RidDleZ33/Ratrig-VC3.1-EazyIDEX/Crossbow_Cutter_Mods/VC4_Depressor/vc4_y_bumper_depressor_v2_2.png

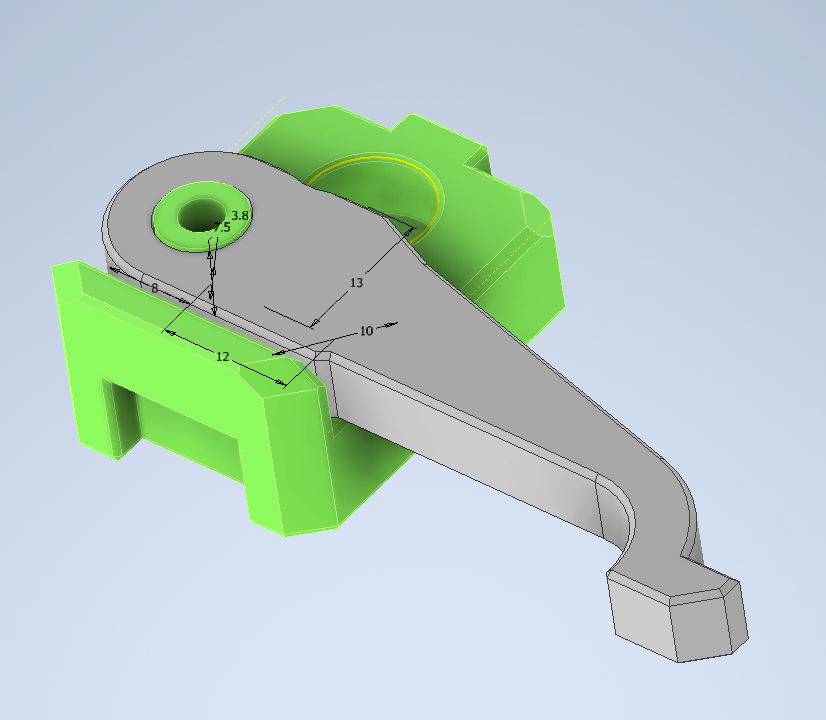
Crossbow_Cutter_Mods/VC4_Depressor/vc4_y_bumper_depressor_v2_2.png
