RidDleZ33/Ratrig-VC3.1-EazyIDEX/Crossbow_Cutter_Mods/VC4_LGX_LITE/20260310_191639.jpg

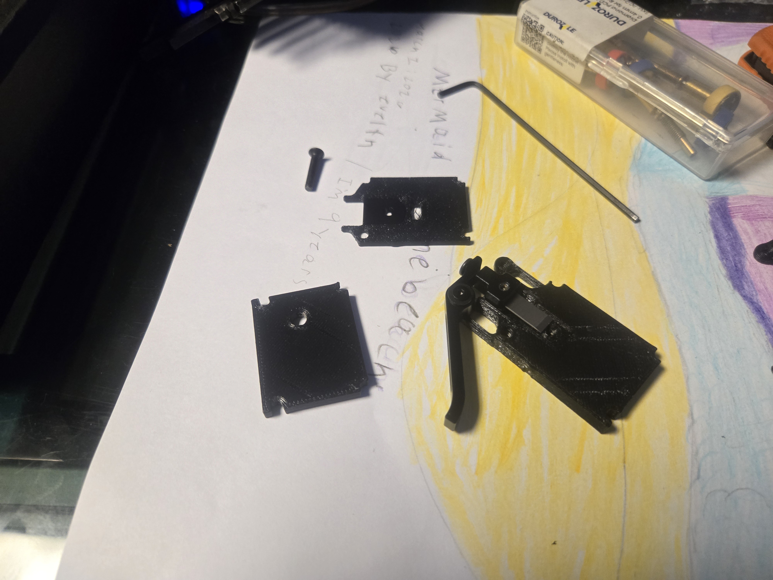
Crossbow_Cutter_Mods/VC4_LGX_LITE/20260310_191639.jpg
