RidDleZ33/Ratrig-VC3.1-EazyIDEX/Crossbow_Cutter_Mods/VC4_LGX_LITE/Cutter_VC4_LGX_LITE_ASSY2.png

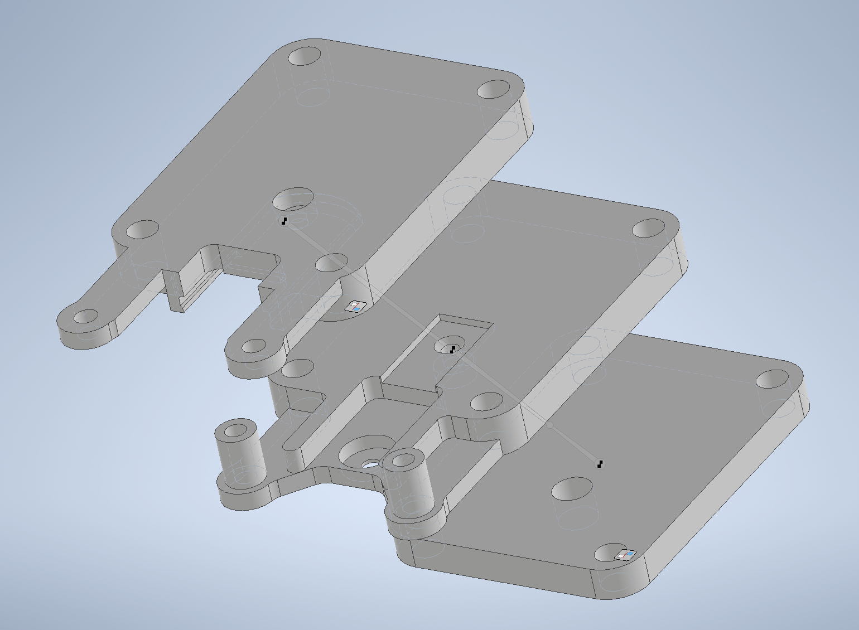
Crossbow_Cutter_Mods/VC4_LGX_LITE/Cutter_VC4_LGX_LITE_ASSY2.png
