RidDleZ33/Ratrig-VC3.1-EazyIDEX/RR_Toolhead_Mods/LGx_Lite_Adapter_MOD/LGx_Lite_REVO1.png

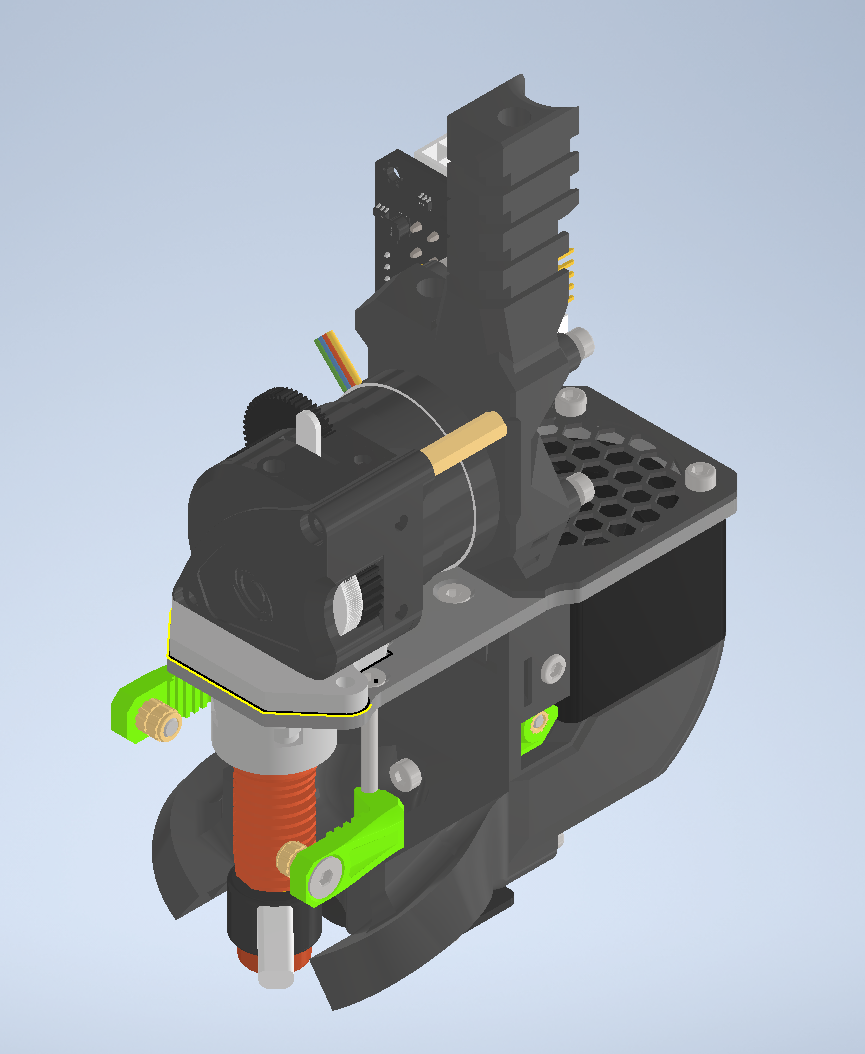
RR_Toolhead_Mods/LGx_Lite_Adapter_MOD/LGx_Lite_REVO1.png
