RidDleZ33/Ratrig-VC3.1-EazyIDEX/3_4_Hybrid/Alum/vc4_xy_joiner_upper_v1.1 v1.stl

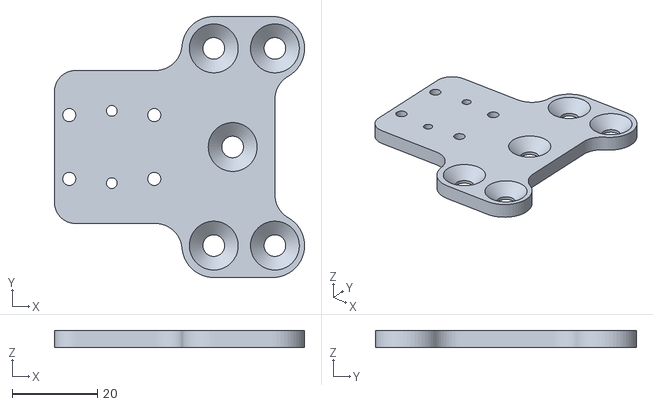
[picture p33: CAD file, 2024-08-03]
3_4_Hybrid/Alum/vc4_xy_joiner_upper_v1.1 v1.stl
58.9 x 61.4 x 4.00
