RidDleZ33/Ratrig-VC3.1-EazyIDEX/Crossbow_Cutter_Mods/VC4_LGX_LITE/Crossbow CNC VC4_LGX_LITE_UNI_V2_Body.stl

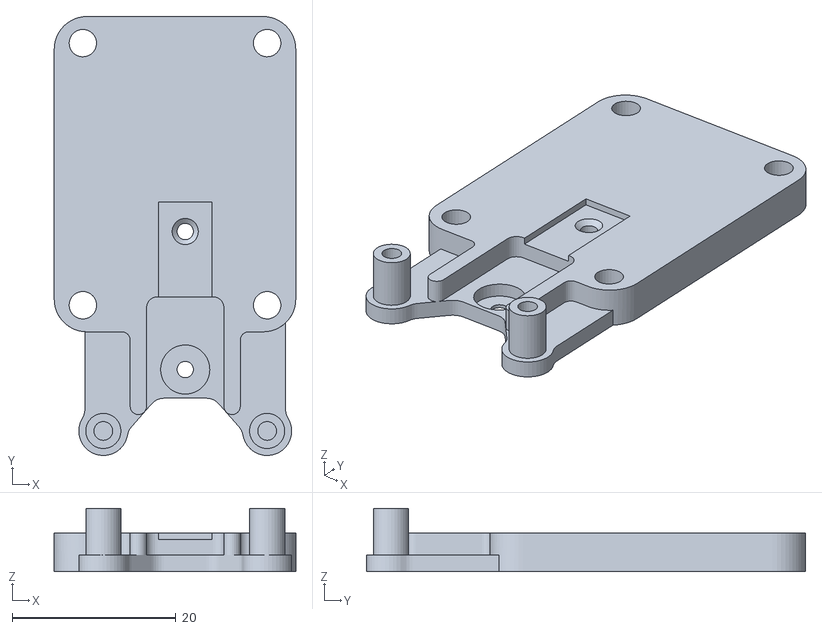
[picture p34: CAD file, 2026-04-05]
Crossbow_Cutter_Mods/VC4_LGX_LITE/Crossbow CNC VC4_LGX_LITE_UNI_V2_Body.stl
29.5 x 53.6 x 7.70
