RidDleZ33/Ratrig-VC3.1-EazyIDEX/VC3.1_Stock/EazyIDEX_enclosure2_xy_idlers_right_idex_3.1.stl

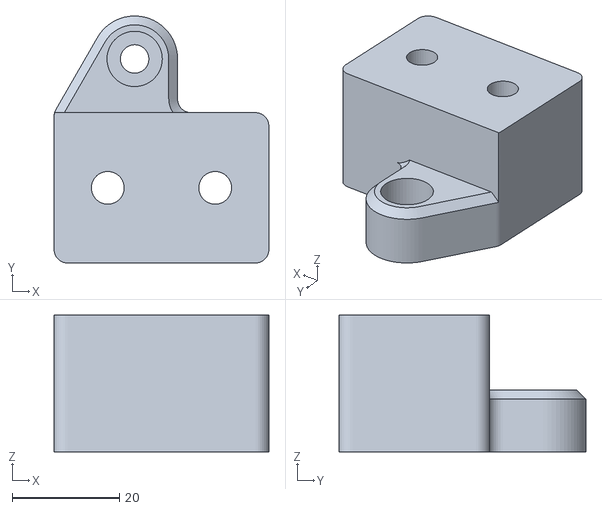
[picture p35: CAD file, 2024-07-27]
VC3.1_Stock/EazyIDEX_enclosure2_xy_idlers_right_idex_3.1.stl
40.0 x 46.0 x 25.5
