RidDleZ33/Ratrig-VC3.1-EazyIDEX/3_4_Hybrid/Alum/EazyIDEX34_vc4_tensioner_body_left_v1.0 v1.stl

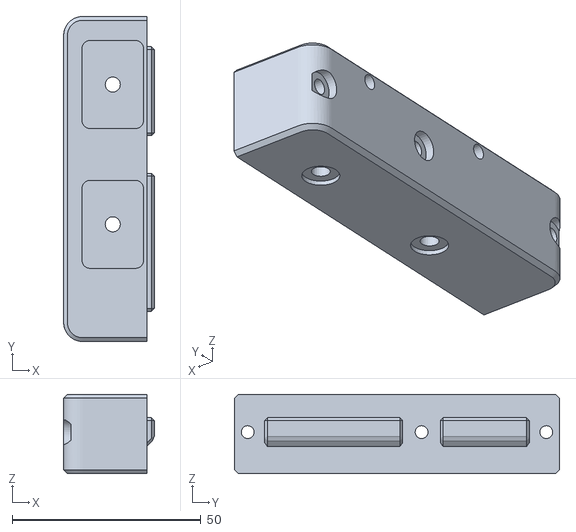
[picture p36: CAD file, 2024-08-03]
3_4_Hybrid/Alum/EazyIDEX34_vc4_tensioner_body_left_v1.0 v1.stl
24.0 x 86.0 x 21.0
