RidDleZ33/Ratrig-VC3.1-EazyIDEX/3_4_Hybrid/vc4_x_endstop v1.stl

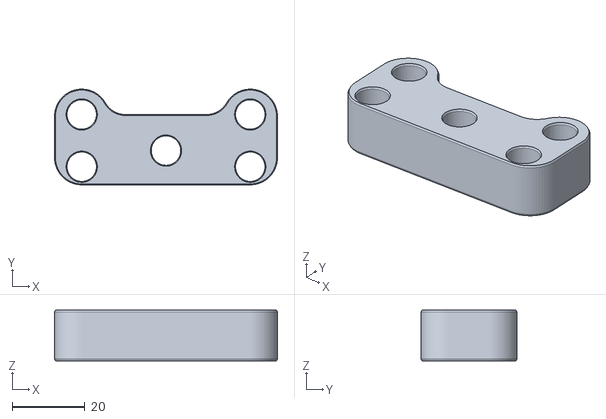
[picture p37: CAD file, 2024-08-03]
3_4_Hybrid/vc4_x_endstop v1.stl
61.4 x 26.4 x 14.0
