RidDleZ33/Ratrig-VC3.1-EazyIDEX/3_4_Hybrid/vc4_y_bumper v1.stl

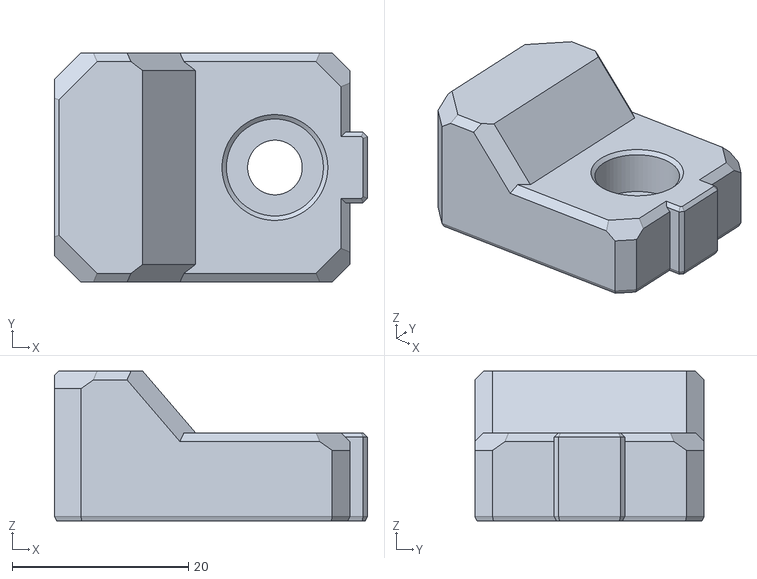
[picture p38: CAD file, 2024-08-03]
3_4_Hybrid/vc4_y_bumper v1.stl
35.5 x 26.0 x 17.0
