RidDleZ33/Ratrig-VC3.1-EazyIDEX/VC3.1_Stock/EazyIDEX_joiner_left.stl

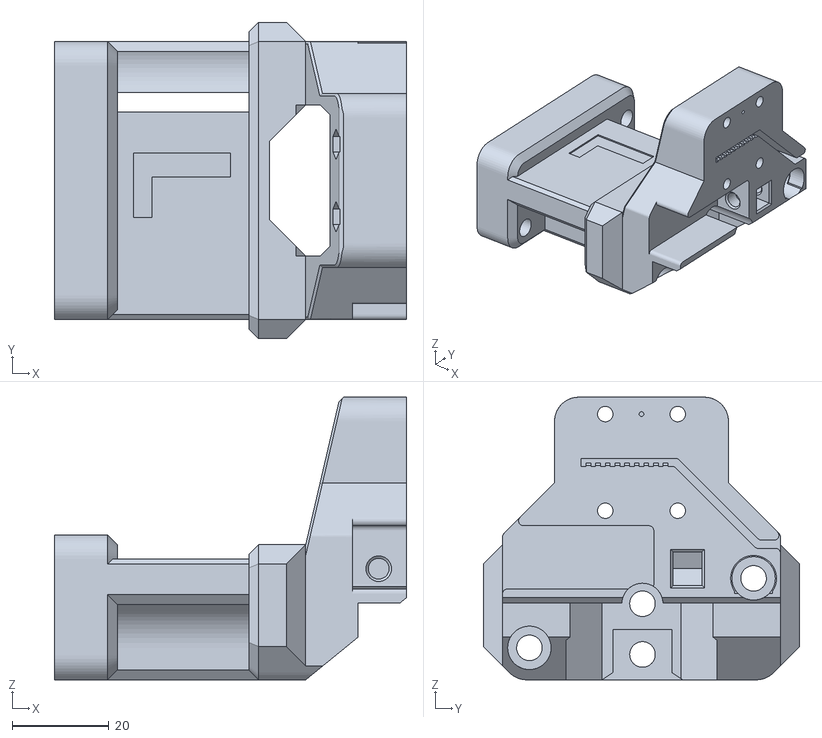
[picture p41: CAD file, 2024-07-27]
VC3.1_Stock/EazyIDEX_joiner_left.stl
72.9 x 65.5 x 58.5
