RidDleZ33/Ratrig-VC3.1-EazyIDEX/3_4_Hybrid/Alum/vc3_idex_motor_plate_v1.0 v2.stl

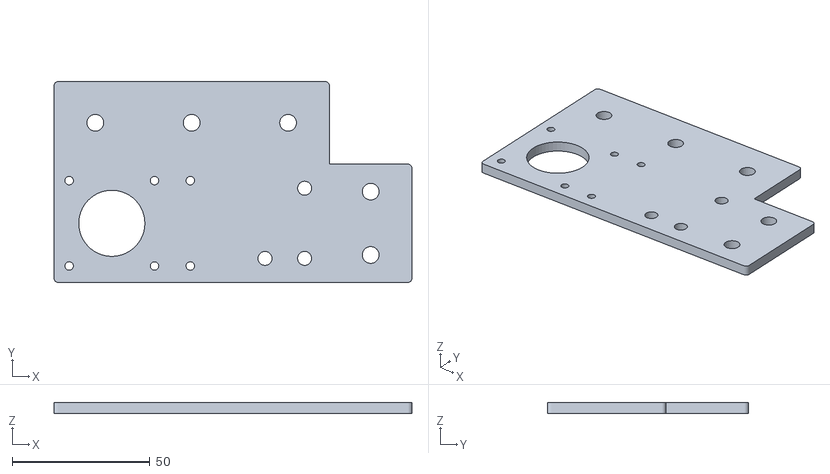
[picture p42: CAD file, 2024-07-28]
3_4_Hybrid/Alum/vc3_idex_motor_plate_v1.0 v2.stl
130.0 x 73.0 x 4.00
