RidDleZ33/Ratrig-VC3.1-EazyIDEX/3_4_Hybrid/vc4_y_endstop_mount v1.stl

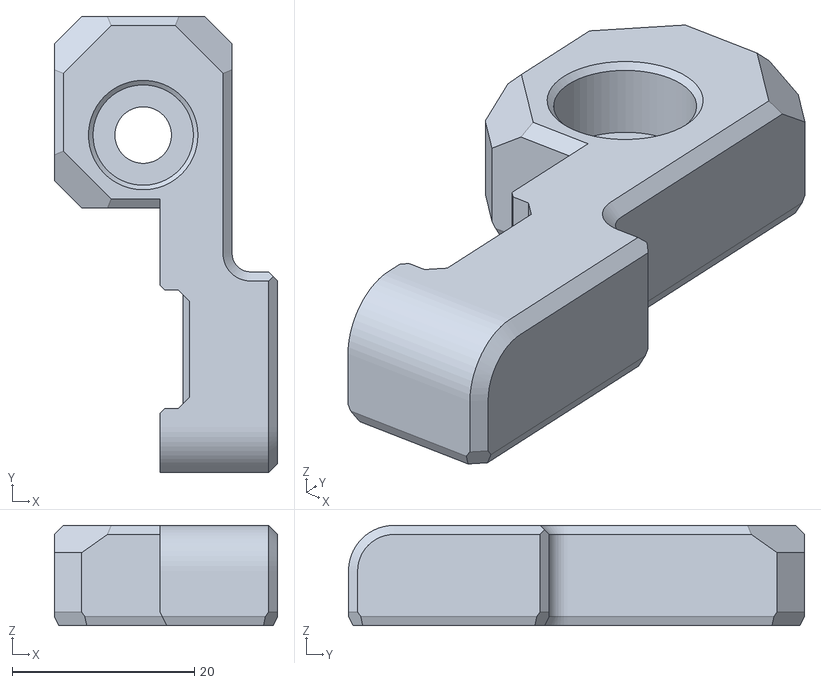
[picture p43: CAD file, 2024-08-03]
3_4_Hybrid/vc4_y_endstop_mount v1.stl
24.5 x 50.0 x 11.0
