RidDleZ33/Ratrig-VC3.1-EazyIDEX/3_4_Hybrid/vc4_y_belt_clamp_cap.stl

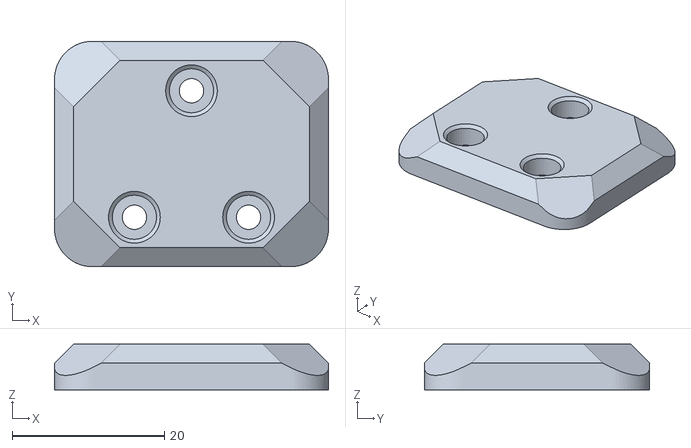
[picture p44: CAD file, 2024-08-03]
3_4_Hybrid/vc4_y_belt_clamp_cap.stl
36.0 x 29.6 x 6.00
