RidDleZ33/Ratrig-VC3.1-EazyIDEX/VC3.1_Stock/EazyIDEX_joiner_lid_left.stl

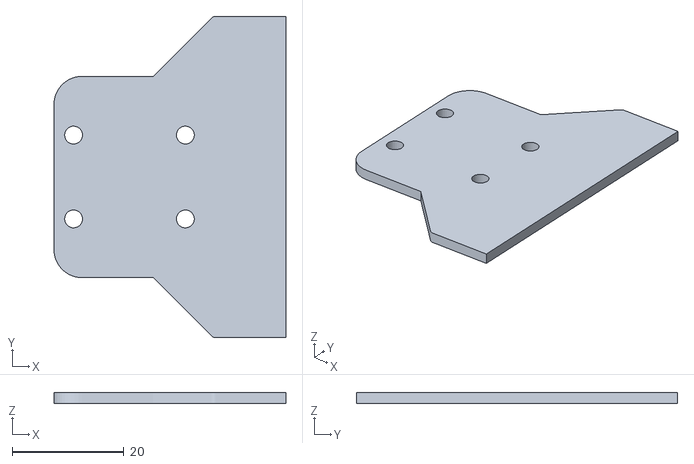
[picture p45: CAD file, 2024-07-27]
VC3.1_Stock/EazyIDEX_joiner_lid_left.stl
41.5 x 57.5 x 2.00
