RidDleZ33/Ratrig-VC3.1-EazyIDEX/3_4_Hybrid/EazyIDEX_Enclosure2_xy_motor_cage_idex_top_right_3.1.stl

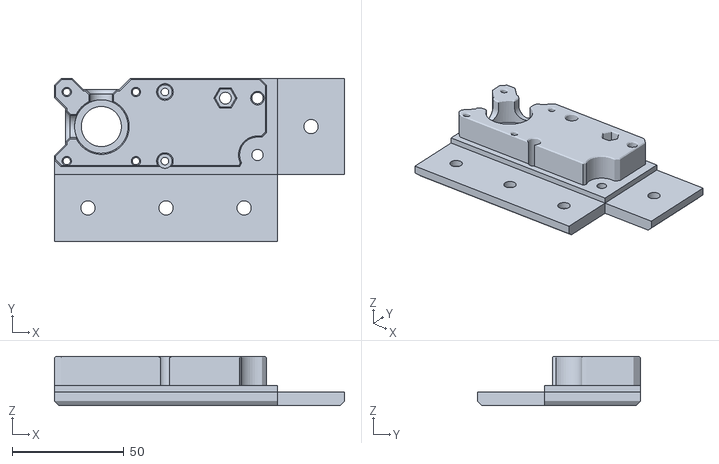
[picture p47: CAD file, 2024-08-03]
3_4_Hybrid/EazyIDEX_Enclosure2_xy_motor_cage_idex_top_right_3.1.stl
130.0 x 73.0 x 22.0
