RidDleZ33/Ratrig-VC3.1-EazyIDEX/3_4_Hybrid/EazyIDEX_y_motor_cage_idex_top_right.stl

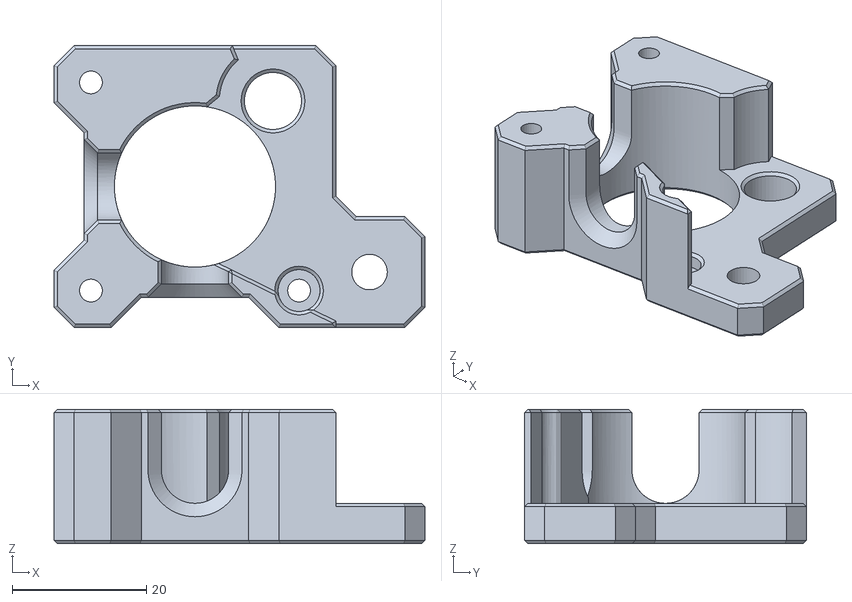
[picture p48: CAD file, 2024-07-27]
3_4_Hybrid/EazyIDEX_y_motor_cage_idex_top_right.stl
55.3 x 42.0 x 20.0
