RidDleZ33/Ratrig-VC3.1-EazyIDEX/3_4_Hybrid/EazyIDEX_y_motor_cage_idex_bottom_right.stl

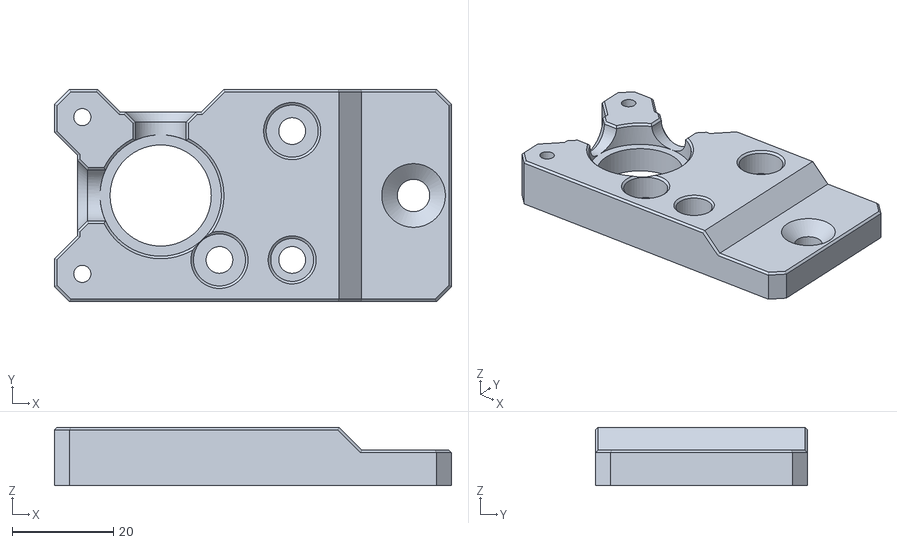
[picture p49: CAD file, 2024-07-27]
3_4_Hybrid/EazyIDEX_y_motor_cage_idex_bottom_right.stl
78.5 x 42.0 x 11.5
