RidDleZ33/Ratrig-VC3.1-EazyIDEX/Crossbow_Cutter_Mods/VC4_Depressor/20260405_195337.jpg

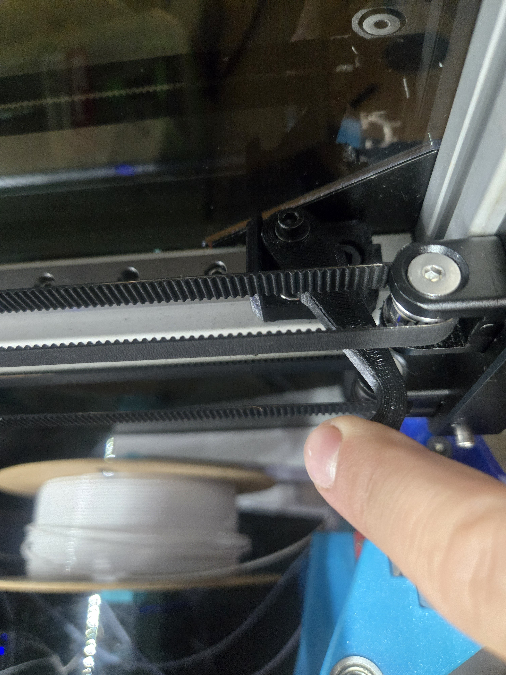
Crossbow_Cutter_Mods/VC4_Depressor/20260405_195337.jpg
